KurtJacobson/alpha-spark/images/detector/20170306_222739.jpg

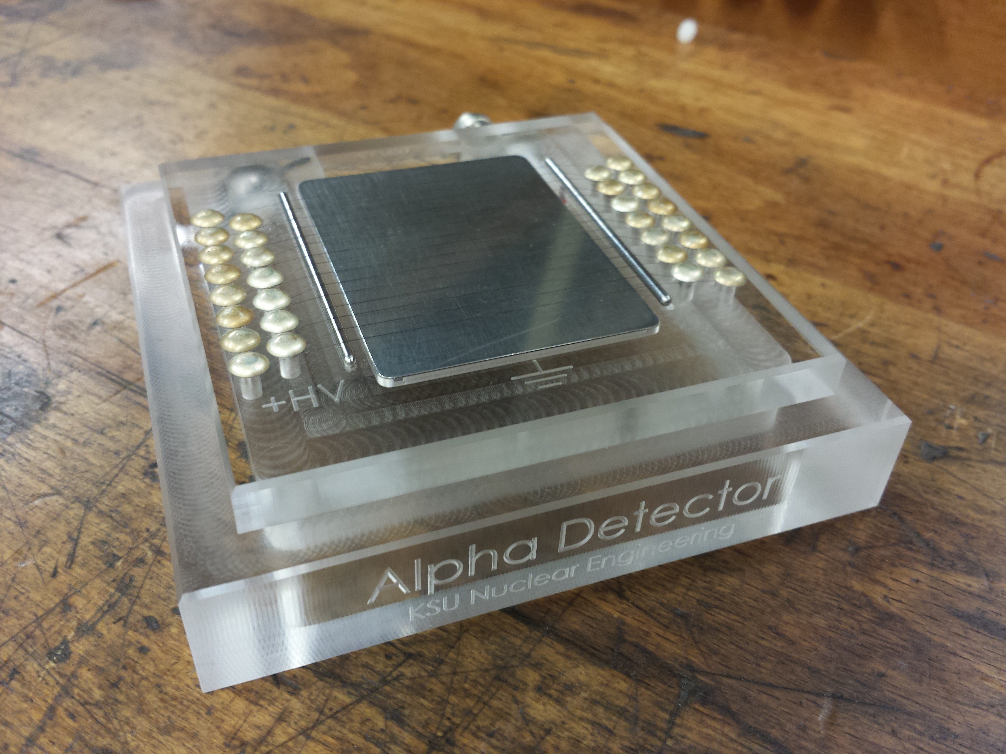
images/detector/20170306_222739.jpg
