KurtJacobson/alpha-spark/images/detector/20170306_222756.jpg

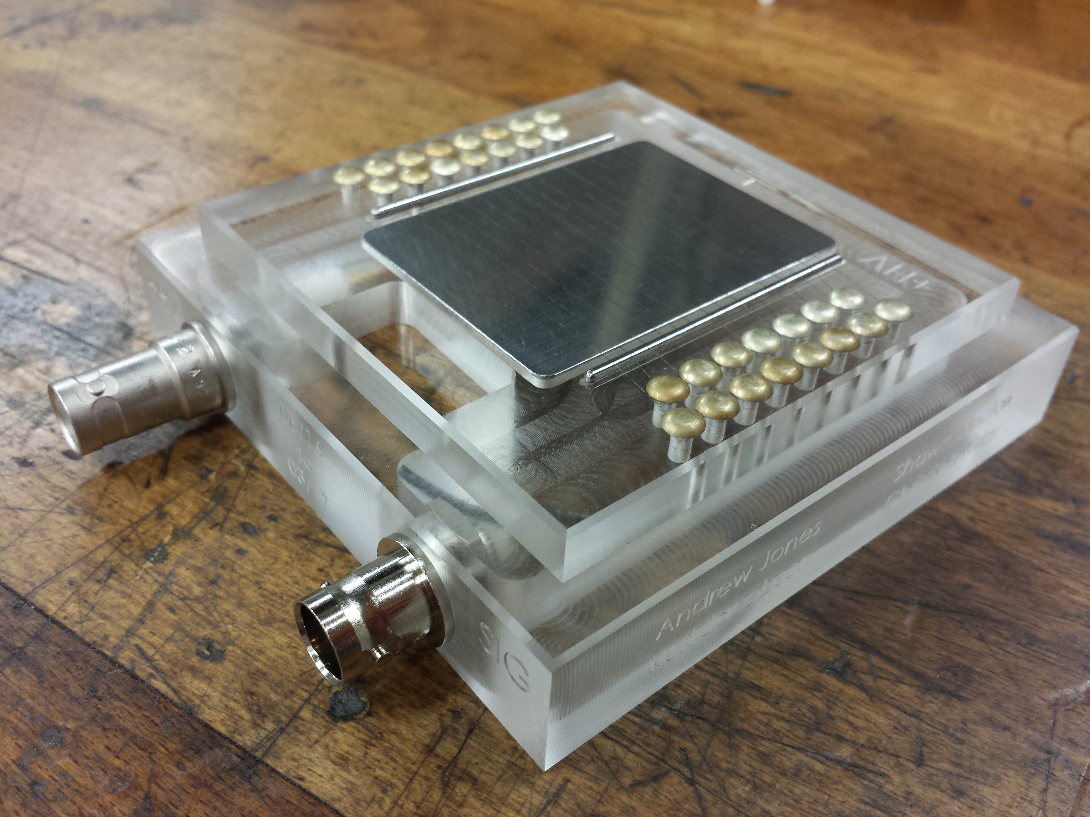
images/detector/20170306_222756.jpg
