KurtJacobson/alpha-spark/images/detector/20170306_222813.jpg

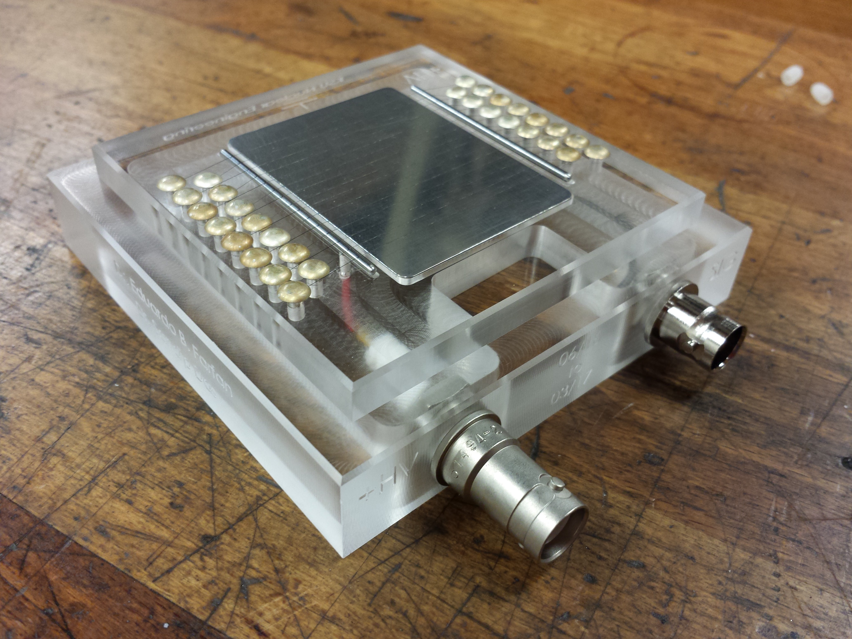
images/detector/20170306_222813.jpg
