KurtJacobson/alpha-spark/images/detector/20170322_160322.jpg

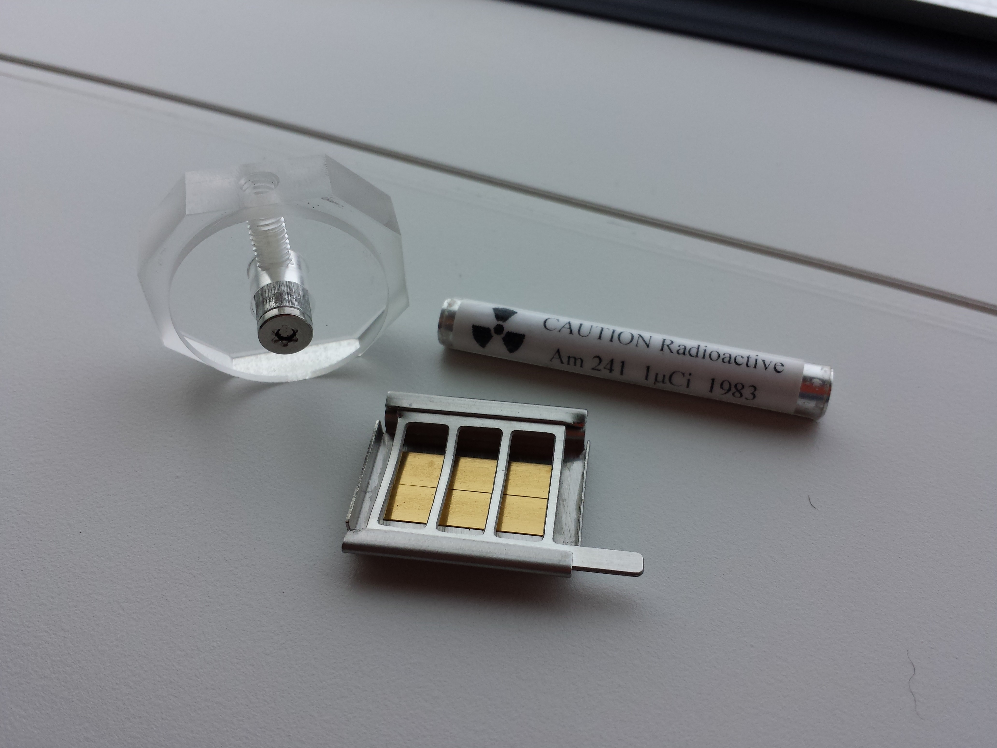
images/detector/20170322_160322.jpg
