KurtJacobson/alpha-spark/images/detector/20170322_160541.jpg

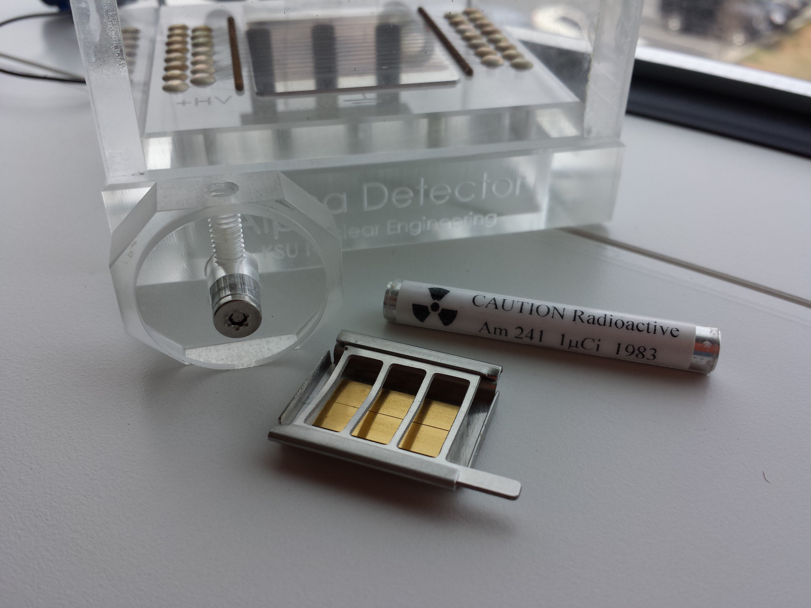
images/detector/20170322_160541.jpg
