KurtJacobson/alpha-spark/images/detector/DSC00182.jpg

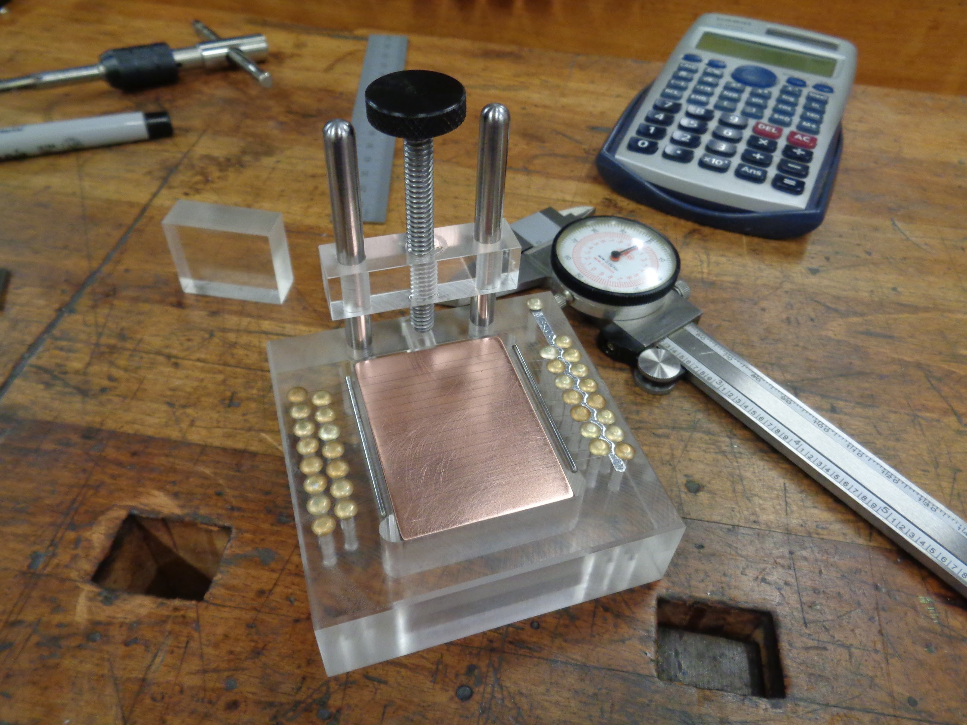
images/detector/DSC00182.jpg
