KurtJacobson/alpha-spark/images/detector/DSC00183.jpg

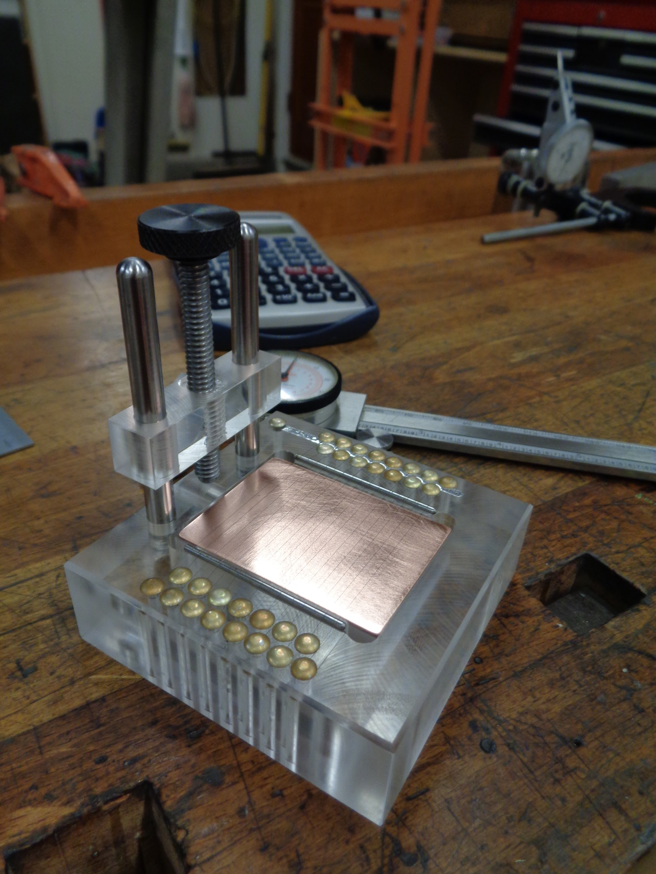
images/detector/DSC00183.jpg
