KurtJacobson/alpha-spark/images/detector/DSC00184.jpg

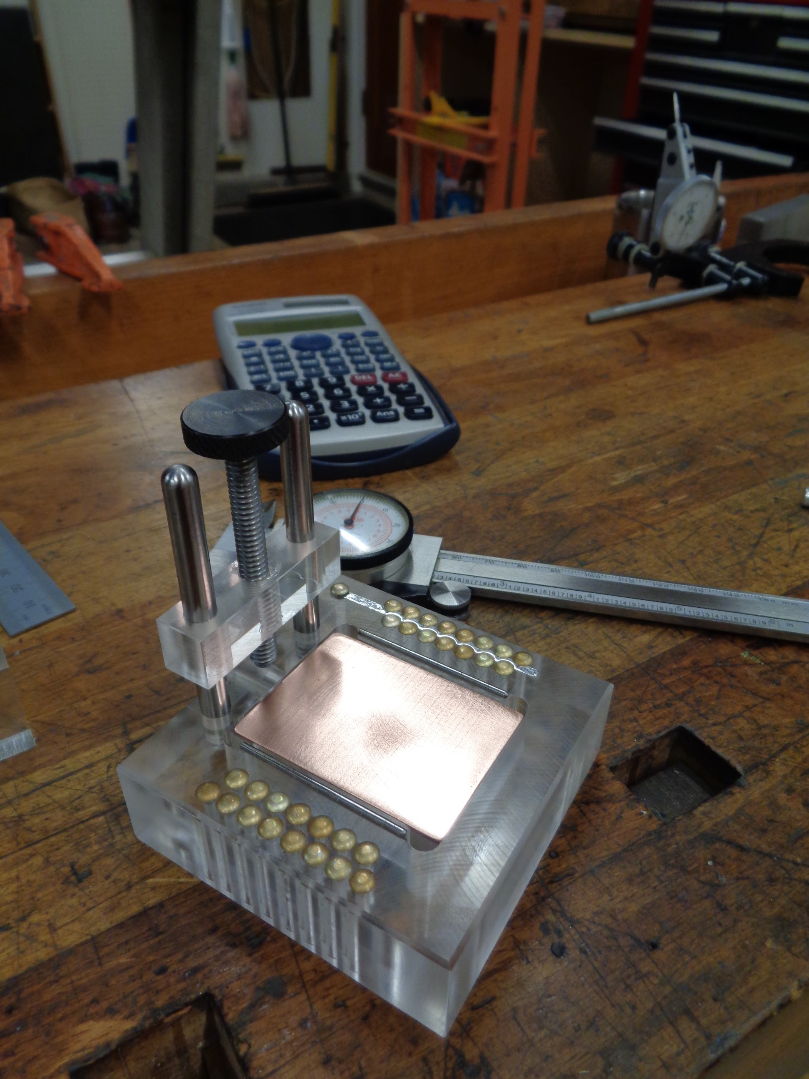
images/detector/DSC00184.jpg
