KurtJacobson/alpha-spark/images/detector/DSC00185.jpg

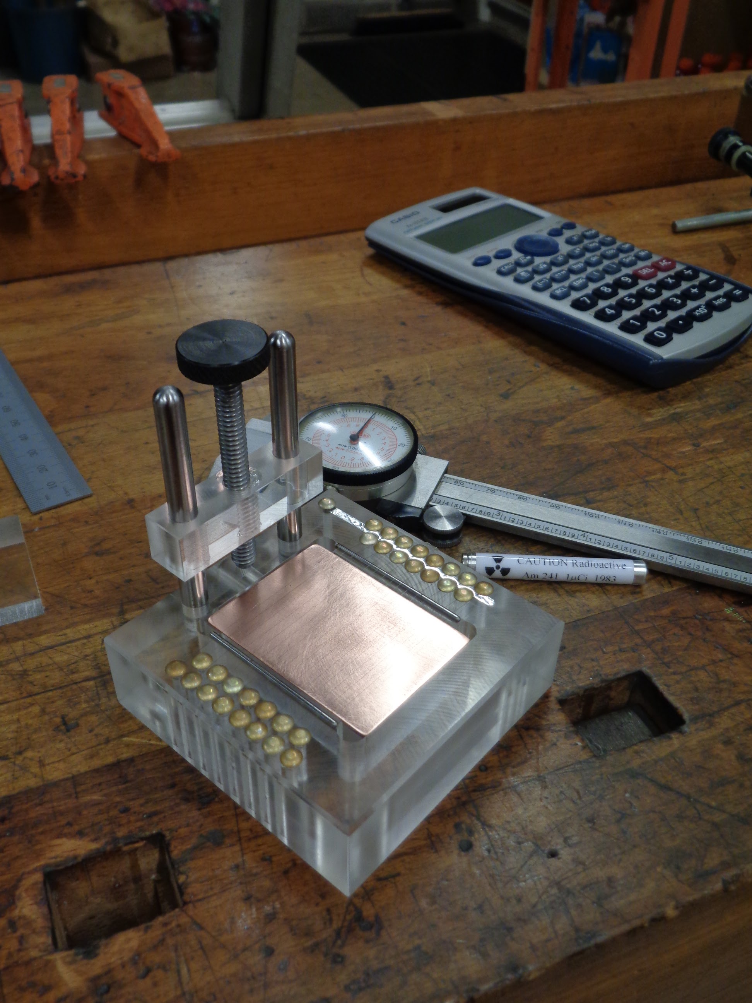
images/detector/DSC00185.jpg
