KurtJacobson/alpha-spark/images/detector/DSC00186.jpg

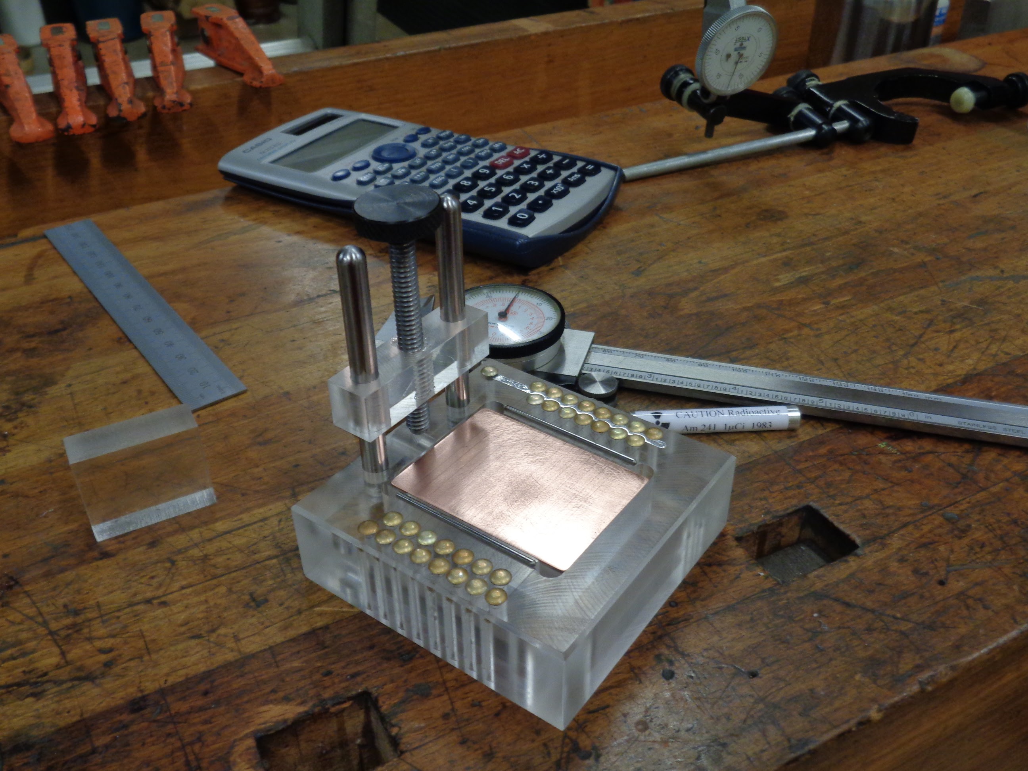
images/detector/DSC00186.jpg
