KurtJacobson/alpha-spark/images/detector/DSC00187.jpg

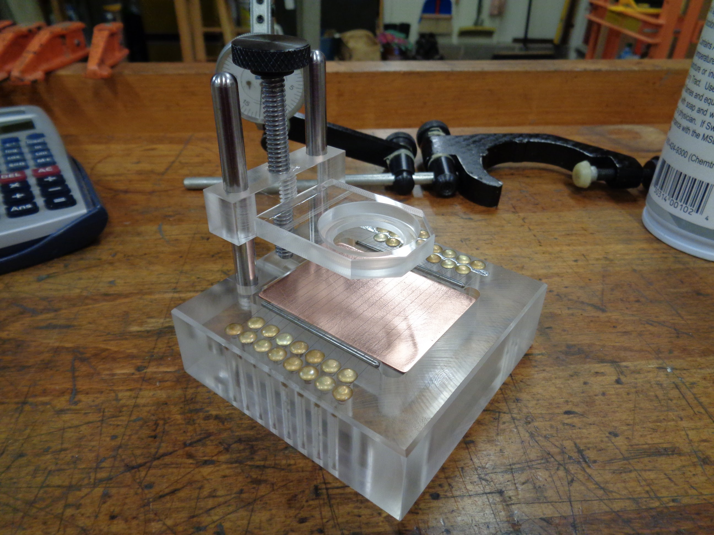
images/detector/DSC00187.jpg
