KurtJacobson/alpha-spark/images/detector/DSC00188.jpg

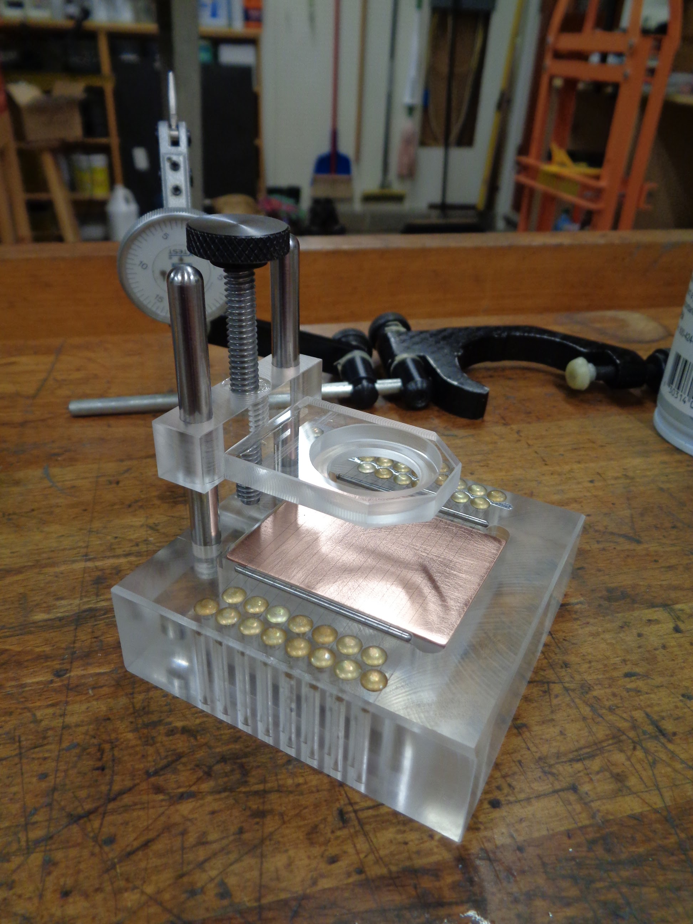
images/detector/DSC00188.jpg
