KurtJacobson/alpha-spark/images/detector/DSC00189.jpg

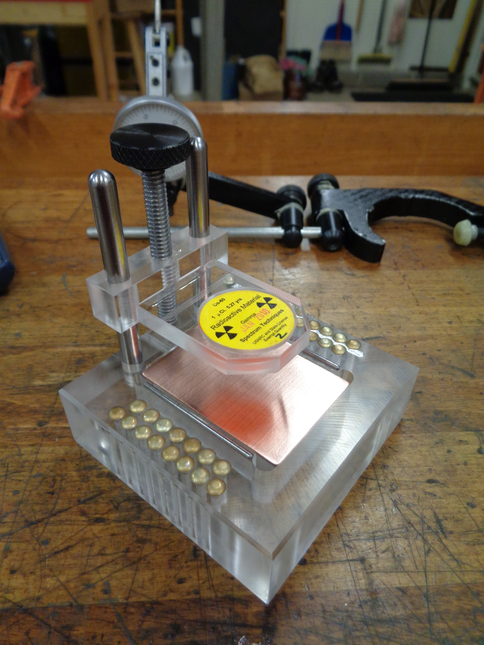
images/detector/DSC00189.jpg
