KurtJacobson/alpha-spark/images/detector/DSC00190.jpg

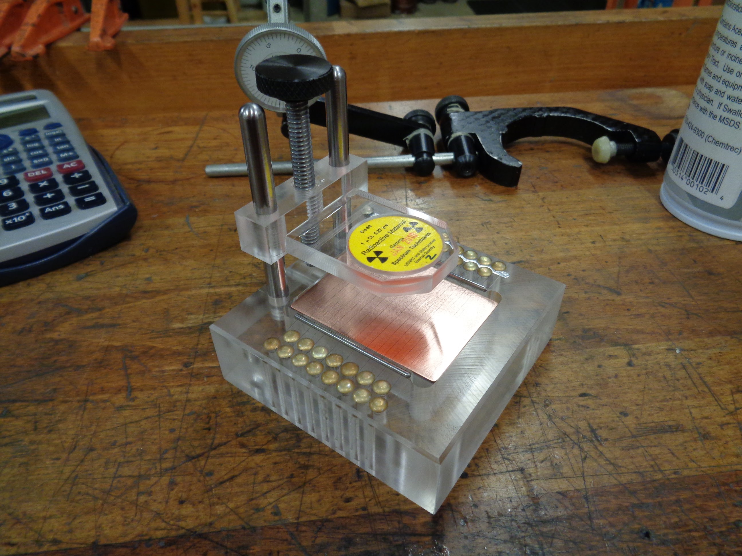
images/detector/DSC00190.jpg
