KurtJacobson/alpha-spark/images/detector/DSC00191.jpg

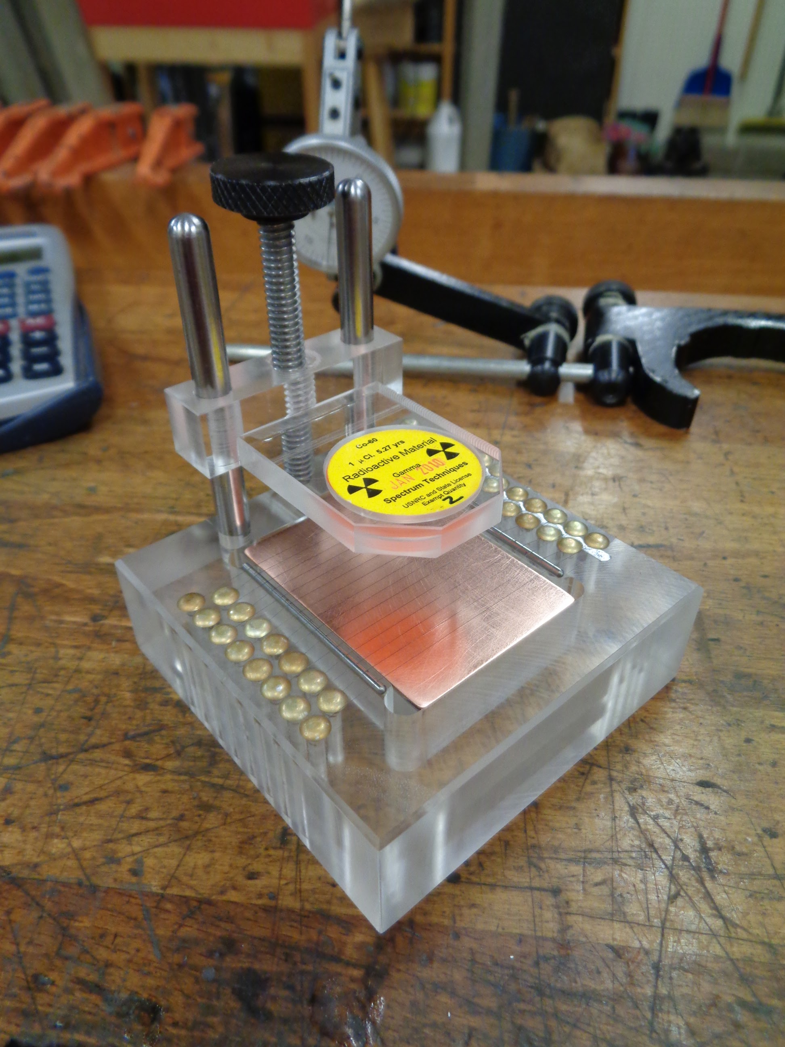
images/detector/DSC00191.jpg
