KurtJacobson/alpha-spark/images/detector/DSC00192.jpg

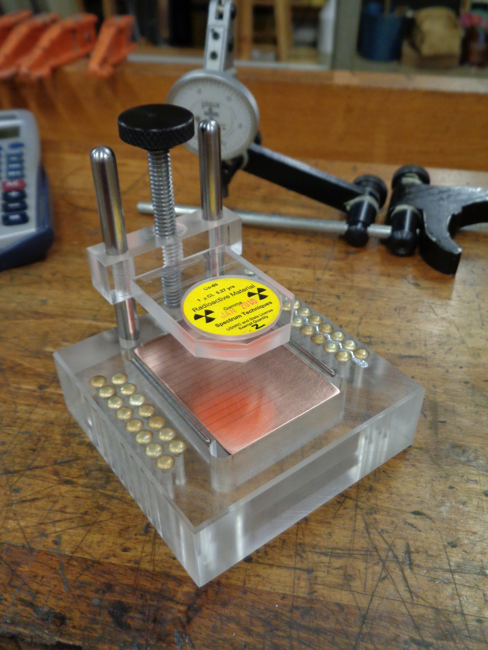
images/detector/DSC00192.jpg
