KurtJacobson/alpha-spark/images/detector/DSC00193.jpg

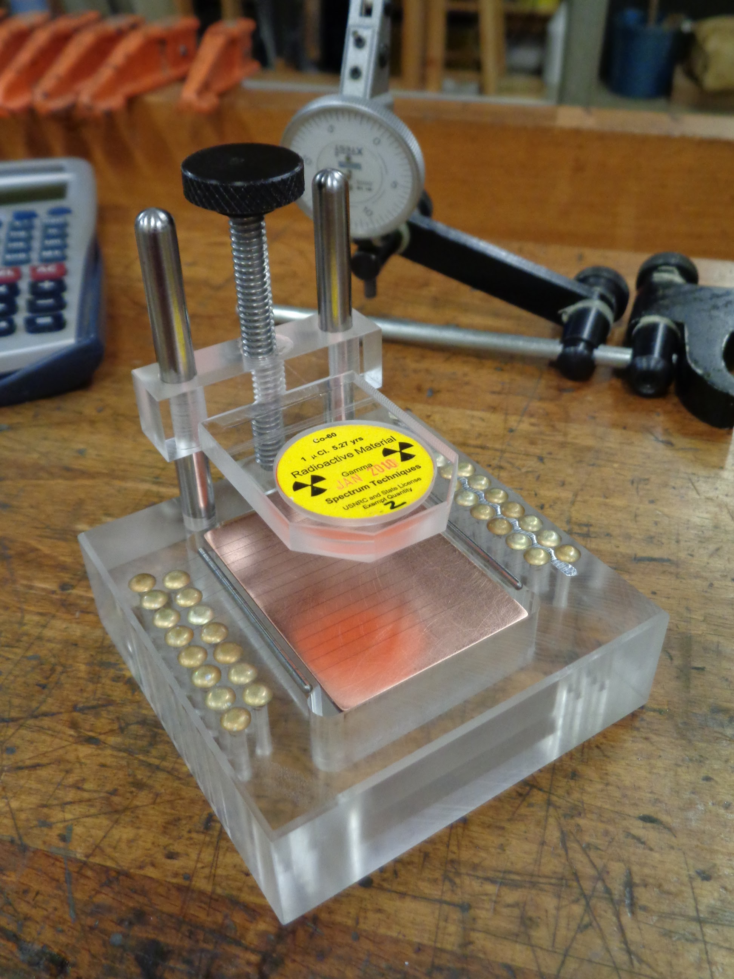
images/detector/DSC00193.jpg
