KurtJacobson/alpha-spark/images/pulses/scope_0.bmp

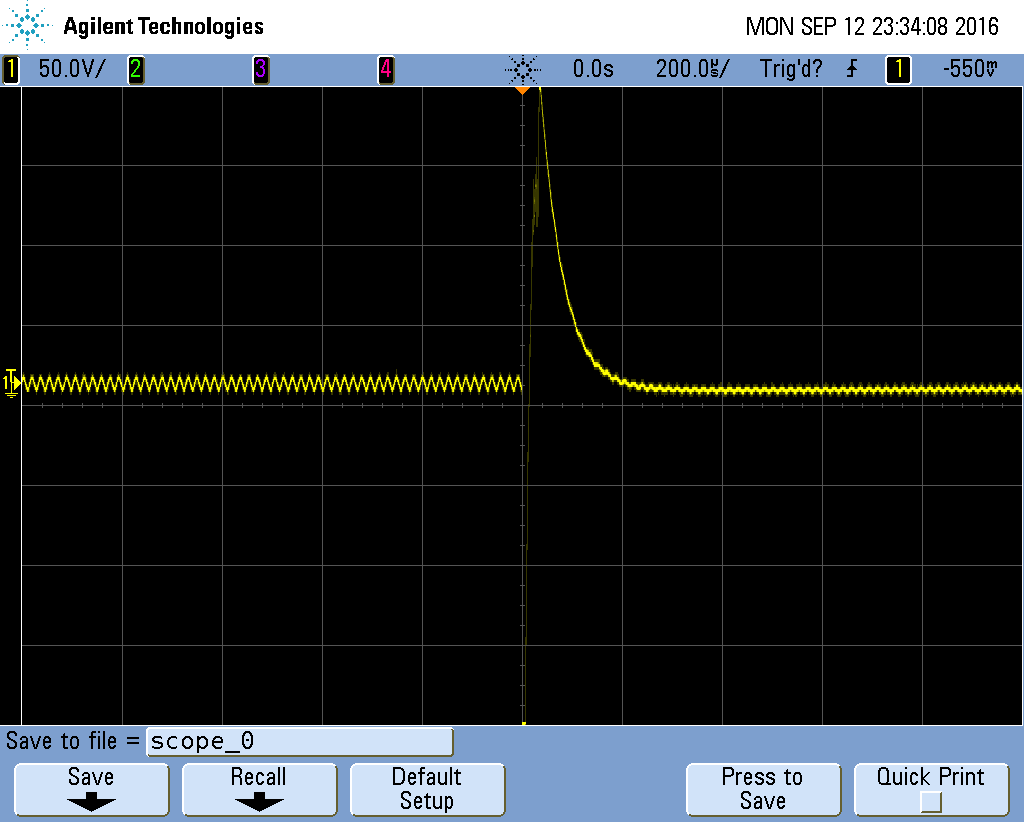
images/pulses/scope_0.bmp
