KurtJacobson/alpha-spark/images/pulses/scope_3.bmp

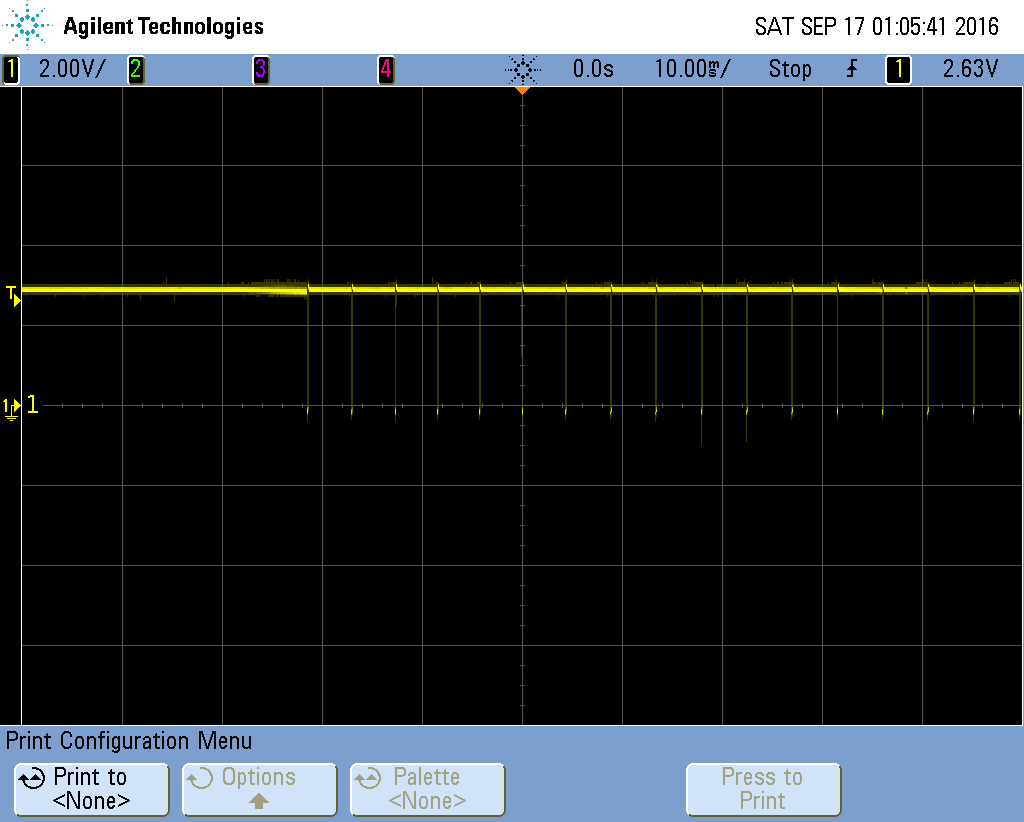
images/pulses/scope_3.bmp
