KurtJacobson/alpha-spark/images/pulses/scope_4.bmp

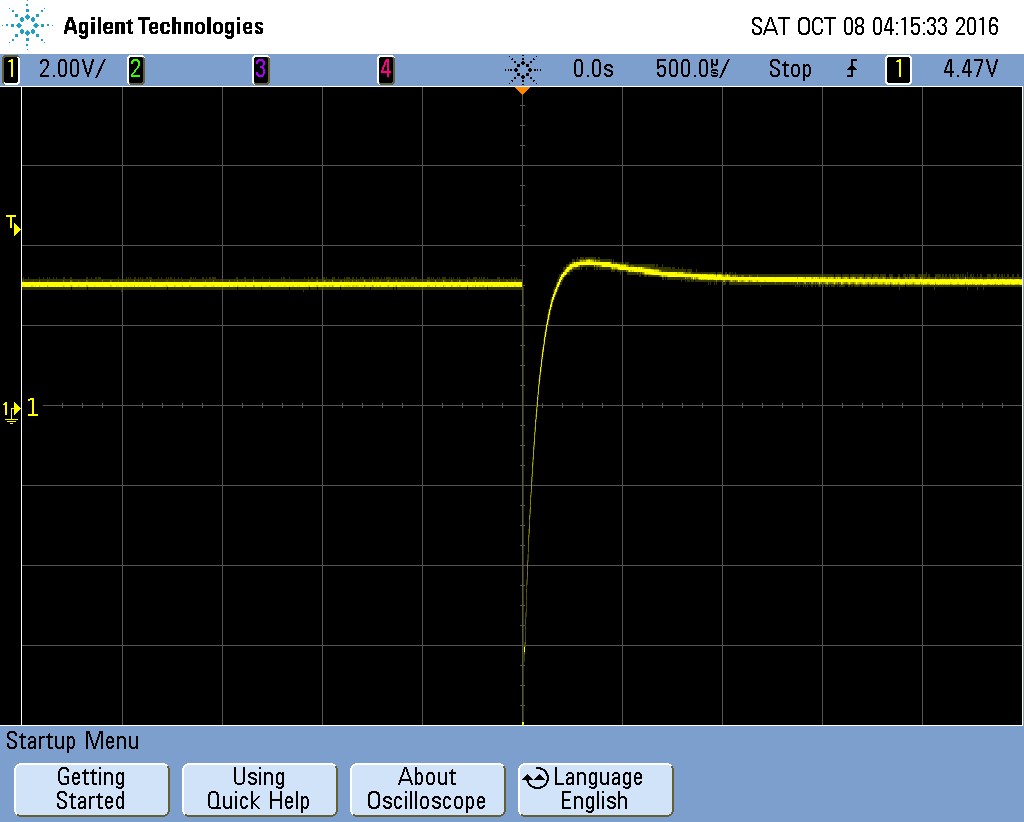
images/pulses/scope_4.bmp
