KurtJacobson/alpha-spark/images/pulses/scope_5.bmp

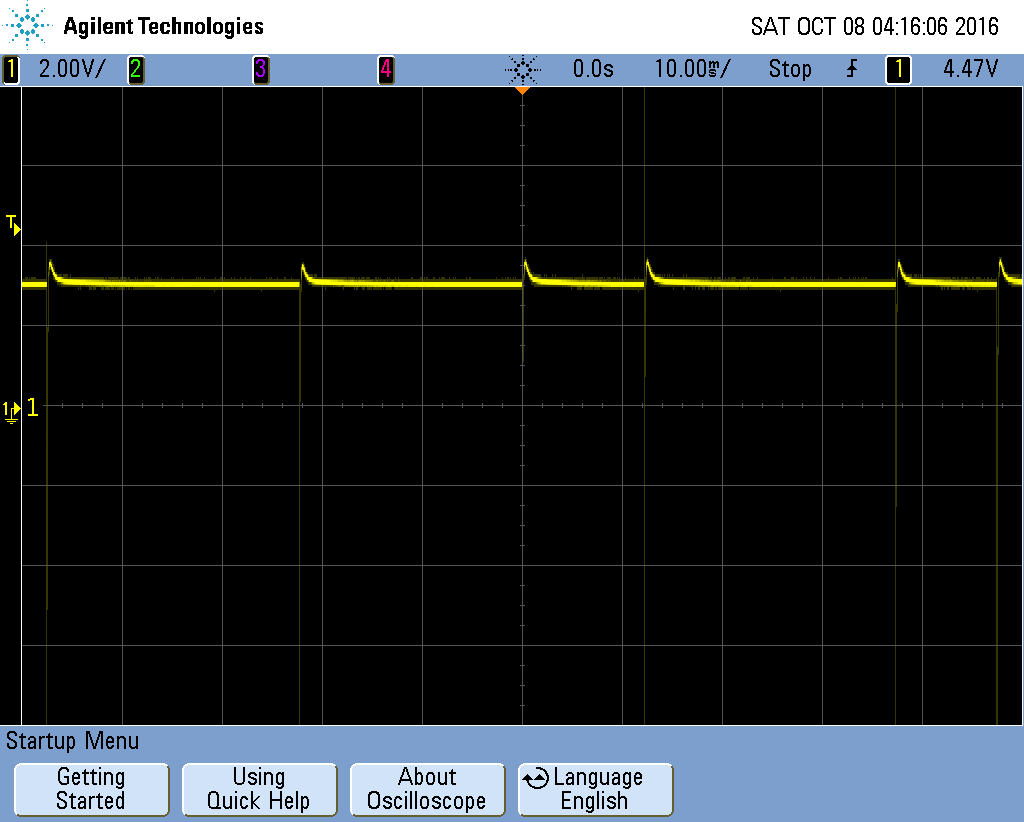
images/pulses/scope_5.bmp
