KurtJacobson/alpha-spark/images/pulses/scope_10.bmp

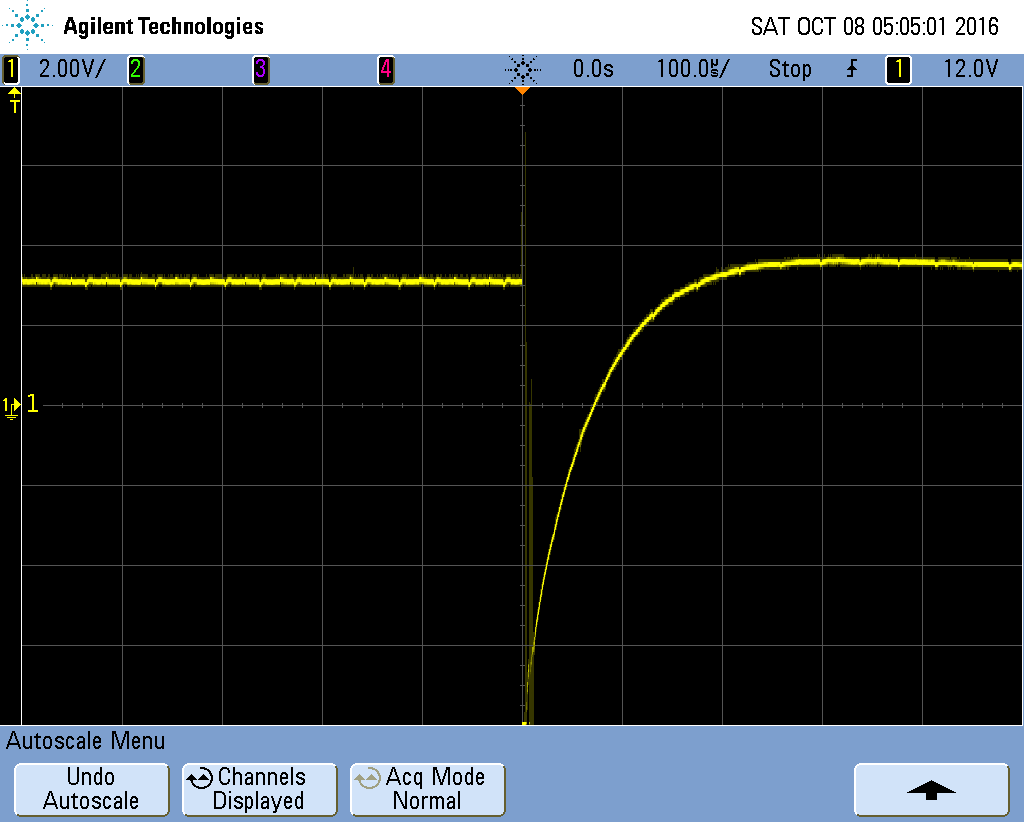
images/pulses/scope_10.bmp
