KurtJacobson/alpha-spark/images/pulses/scope_11.bmp

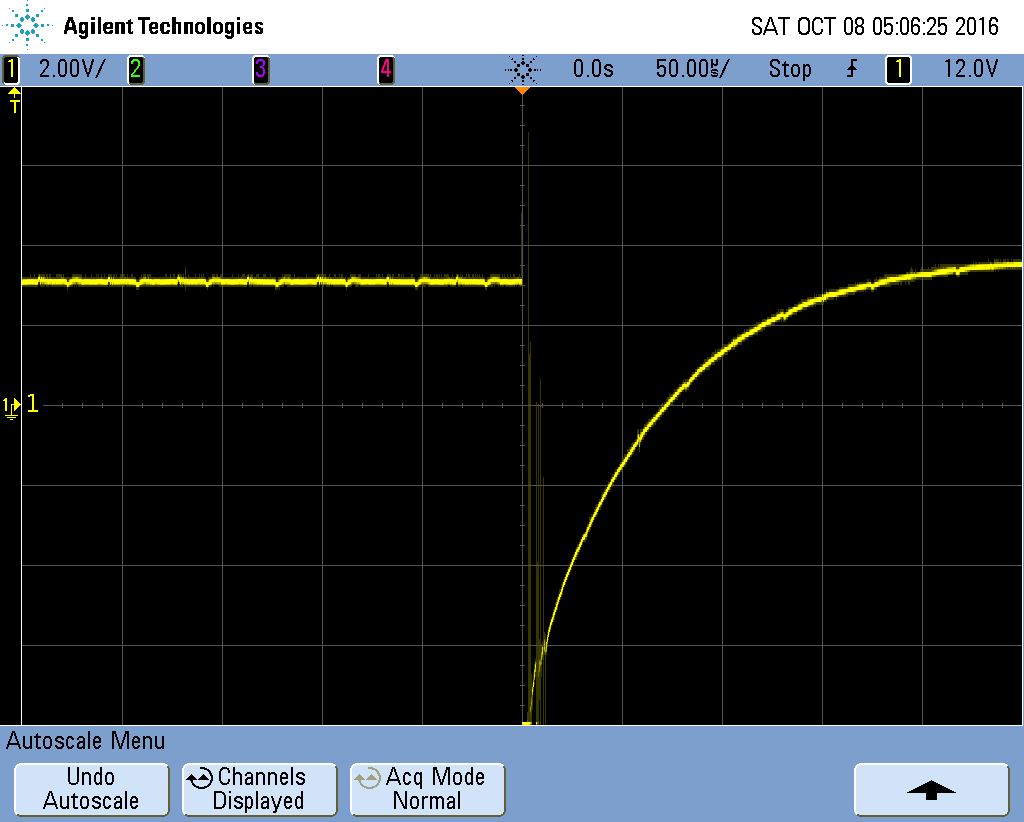
images/pulses/scope_11.bmp
