KurtJacobson/alpha-spark/models/CCS Final.png

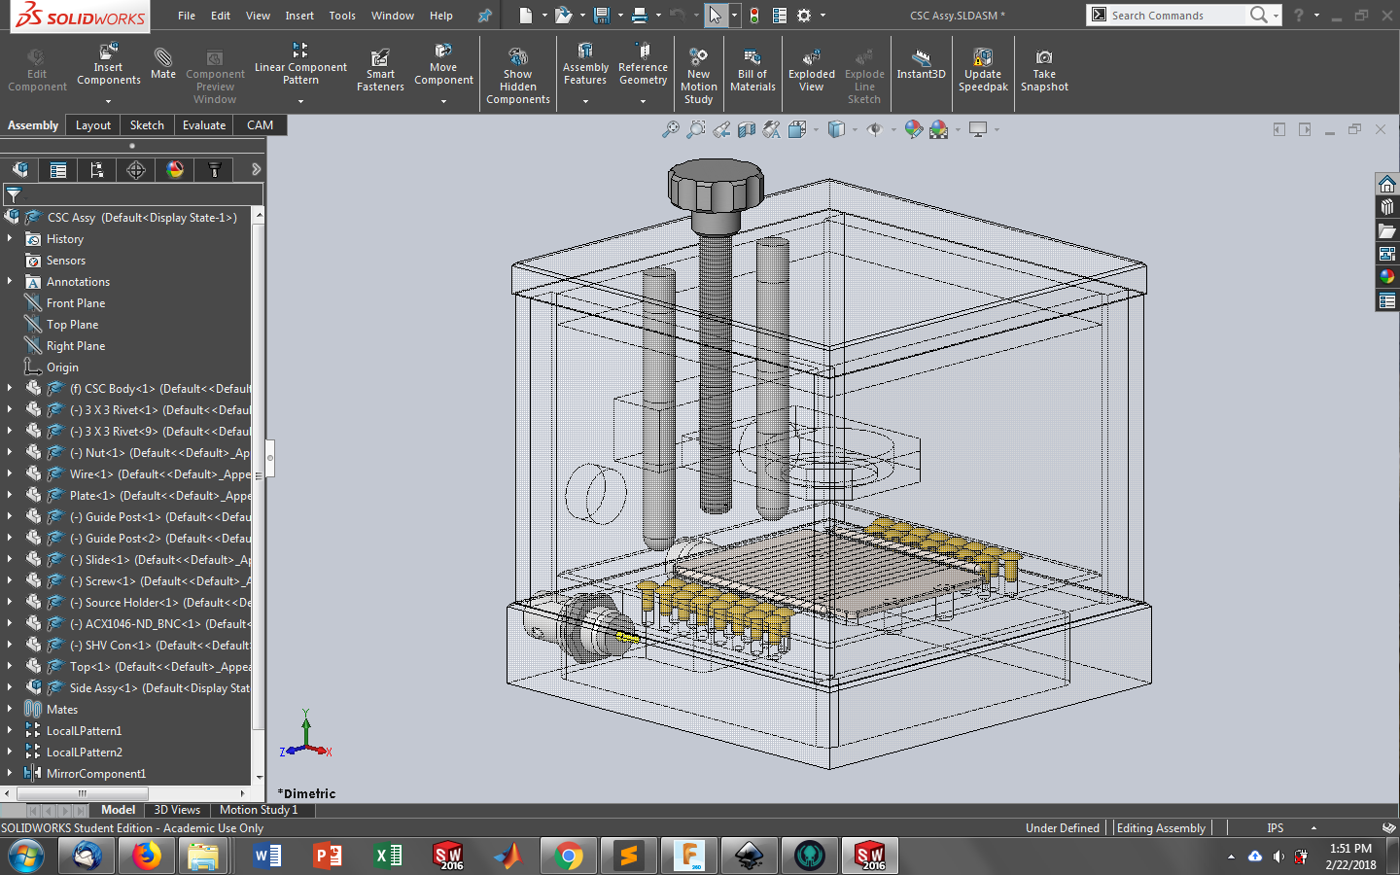
models/CCS Final.png
