KurtJacobson/alpha-spark/models/CCS w Holder Dia.png

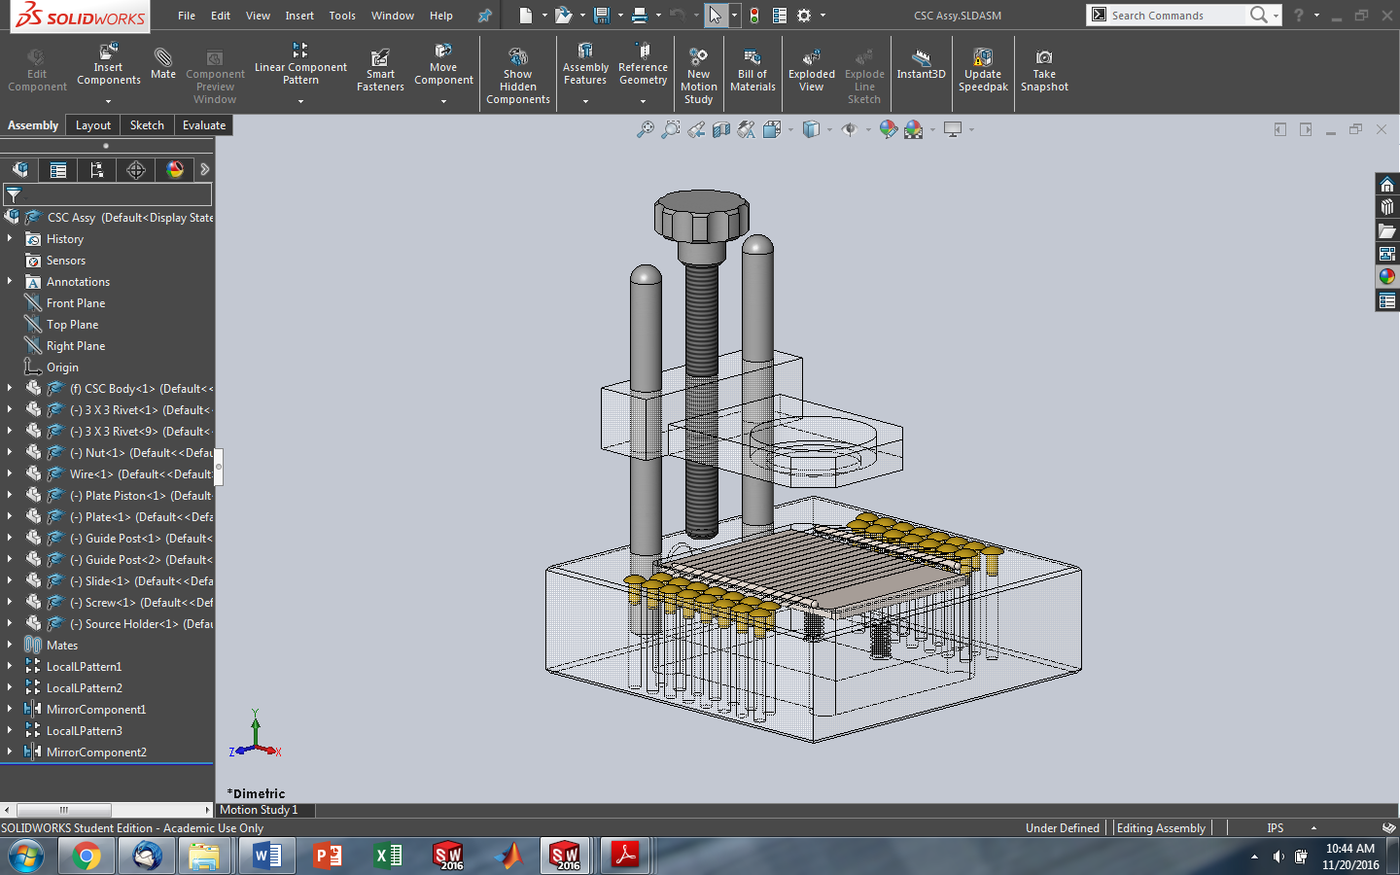
models/CCS w Holder Dia.png
