KurtJacobson/alpha-spark/models/CCS w Holder Iso.png

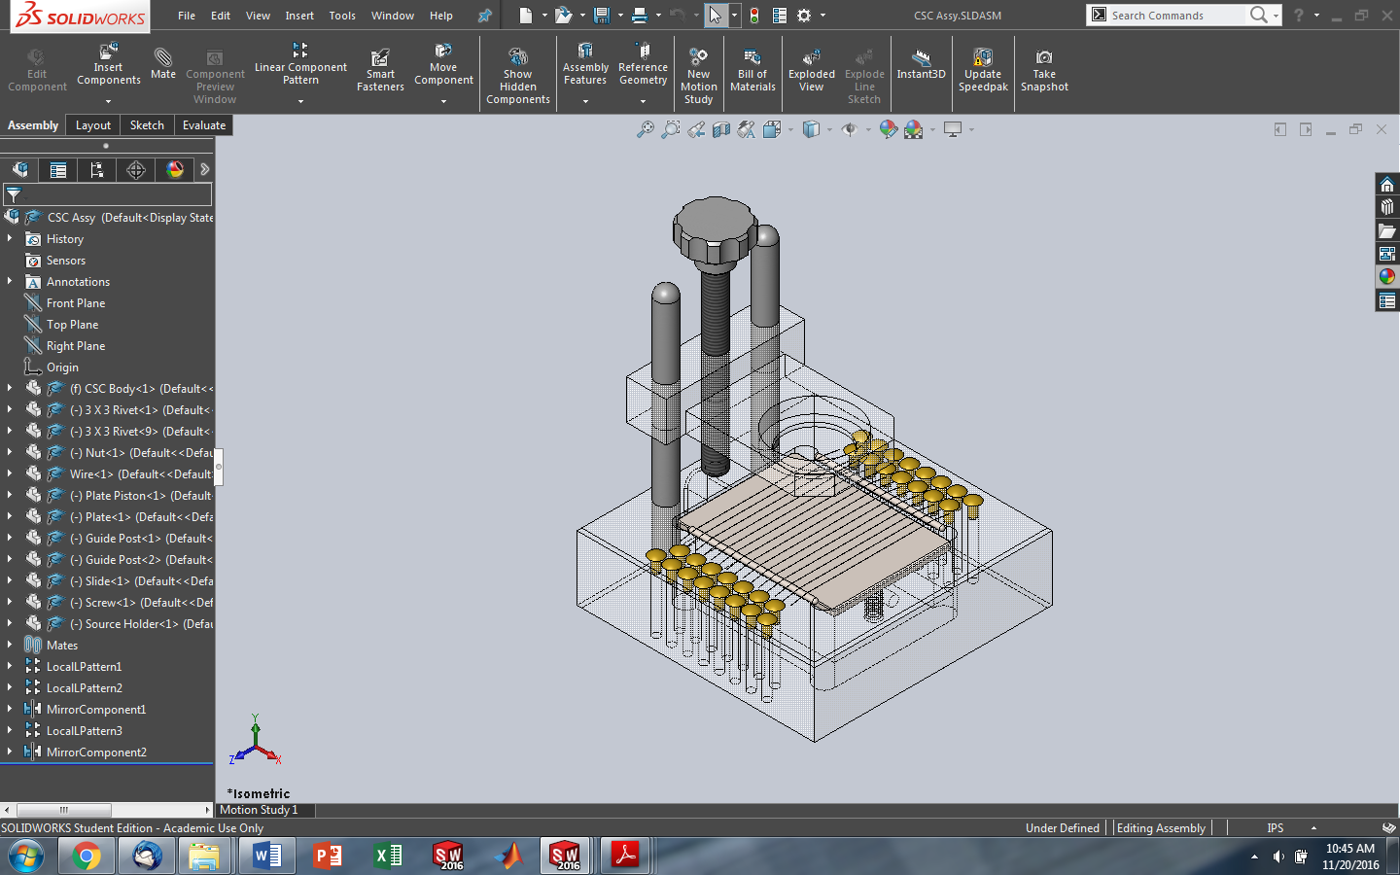
models/CCS w Holder Iso.png
