KurtJacobson/alpha-spark/models/CSC Model Dia.png

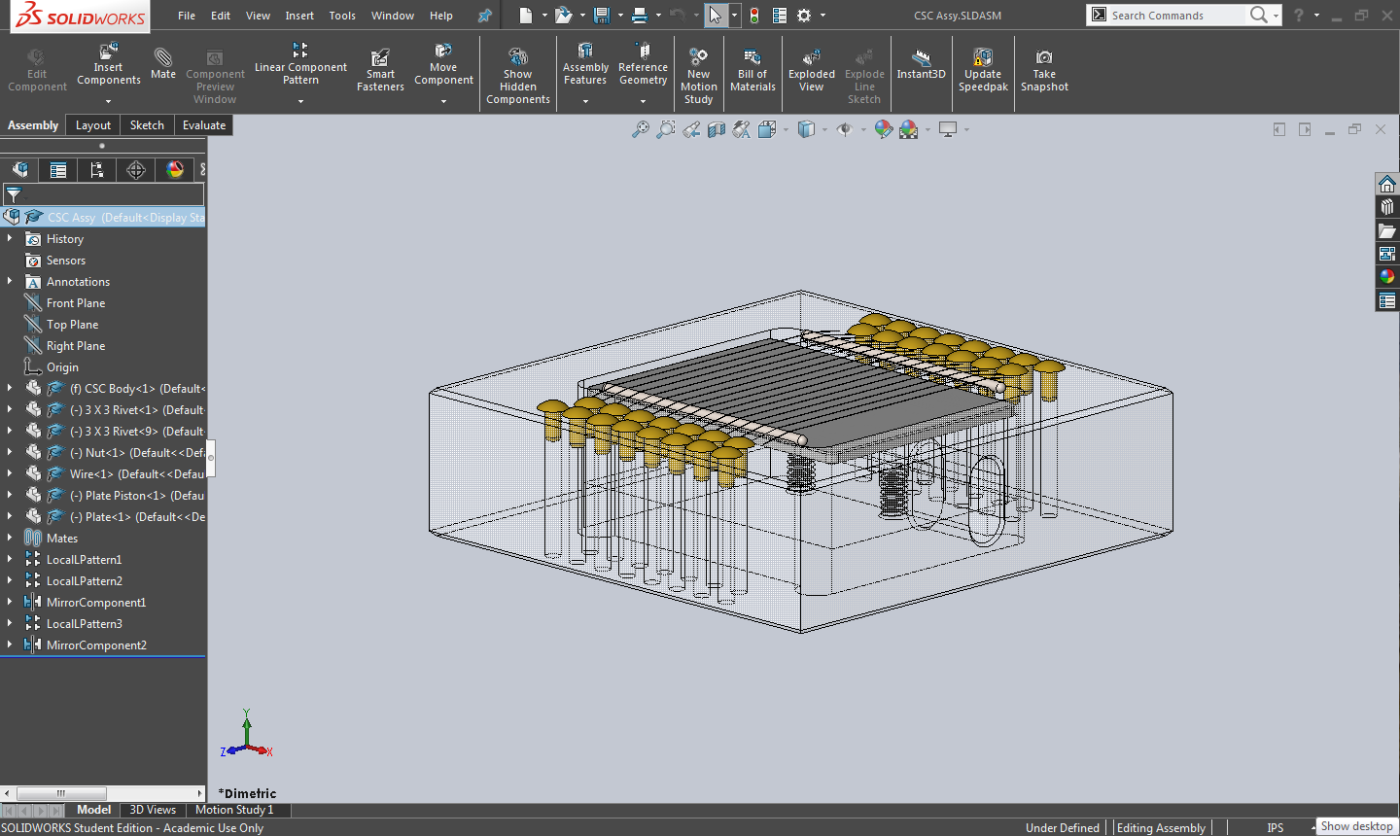
models/CSC Model Dia.png
