KurtJacobson/alpha-spark/models/CSC Model Iso.png

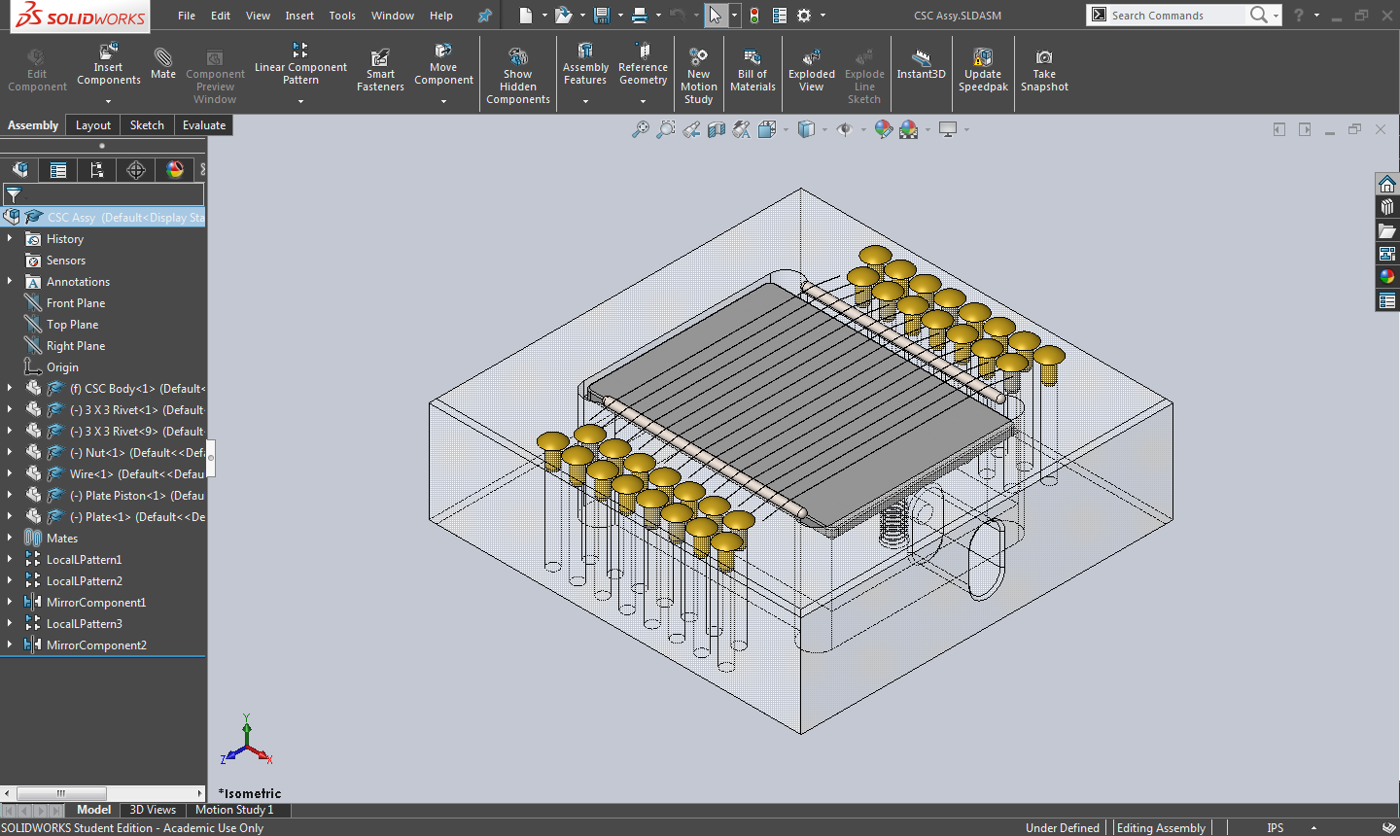
models/CSC Model Iso.png
