KurtJacobson/alpha-spark/models/CSC Render.JPG

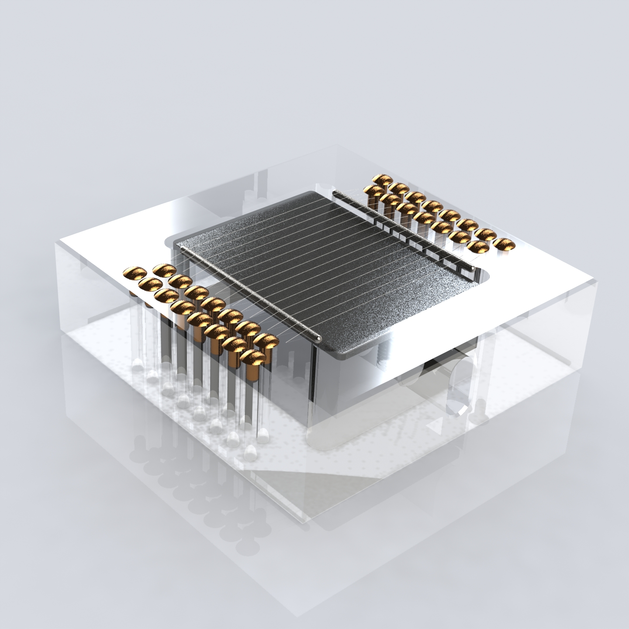
models/CSC Render.JPG
