KurtJacobson/alpha-spark/models/1st Build/Source.SLDPRT

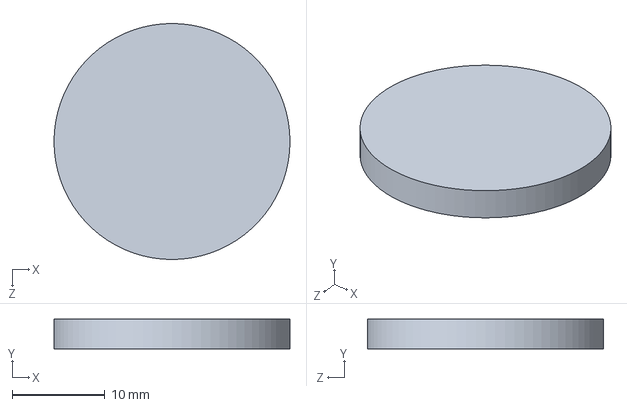
[picture p48: CAD file, 2018-02-22]
models/1st Build/Source.SLDPRT
25.4 x 3.17 x 25.4 mm
