KurtJacobson/alpha-spark/models/2nd Build/Slide.SLDPRT

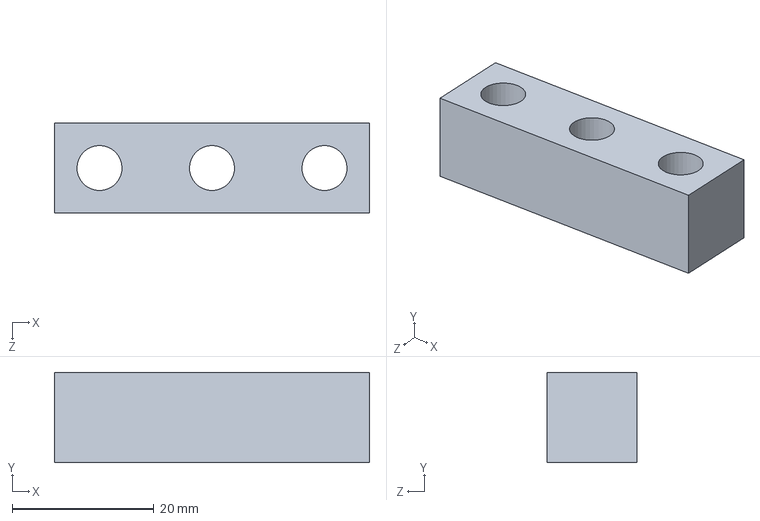
[picture p49: CAD file, 2018-02-22]
models/2nd Build/Slide.SLDPRT
44.5 x 12.7 x 12.7 mm
