KurtJacobson/alpha-spark/models/1st Build/Plate.SLDPRT

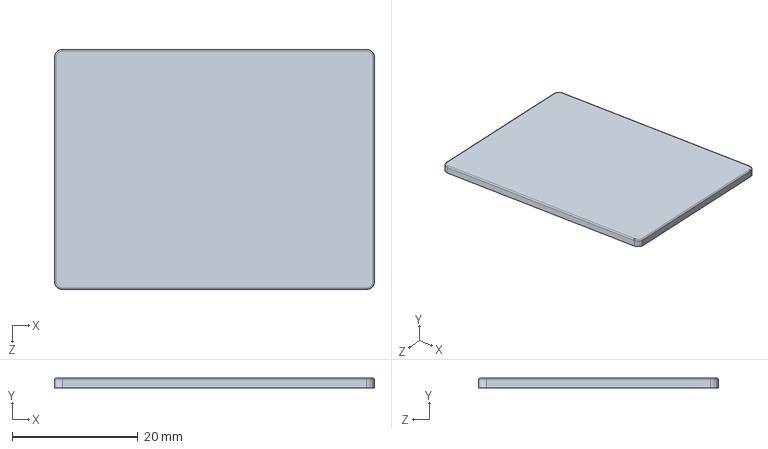
[picture p50: CAD file, 2018-02-22]
models/1st Build/Plate.SLDPRT
50.8 x 1.59 x 38.1 mm
