KurtJacobson/alpha-spark/models/2nd Build/SHV.SLDPRT

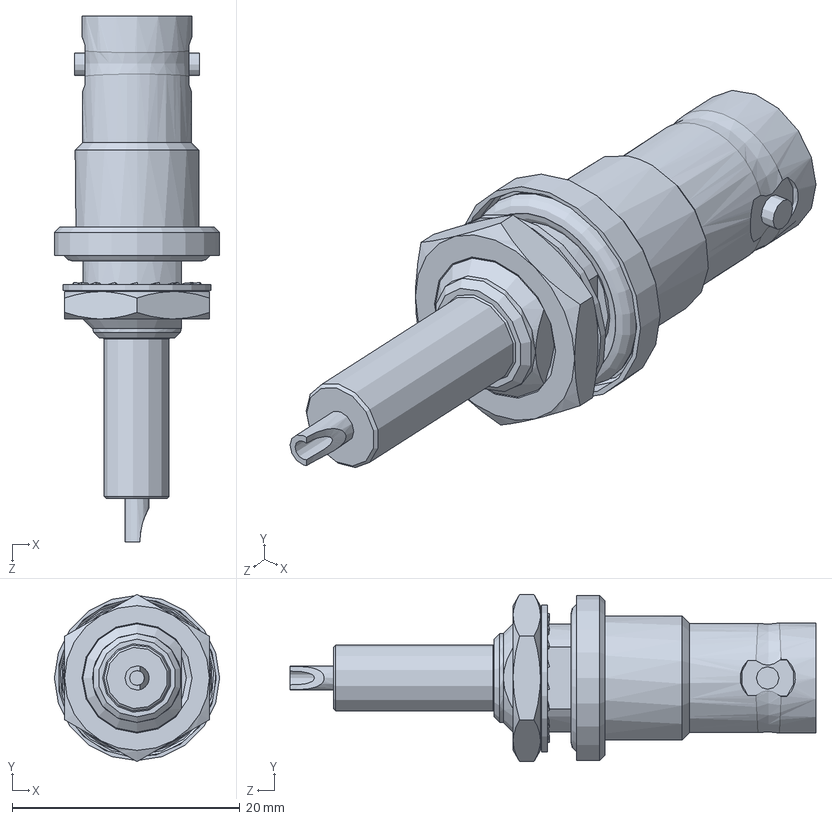
[picture p51: CAD file, 2018-02-22]
models/2nd Build/SHV.SLDPRT
14.5 x 14.7 x 46.1 mm
