KurtJacobson/alpha-spark/models/2nd Build/Top Cover.SLDPRT

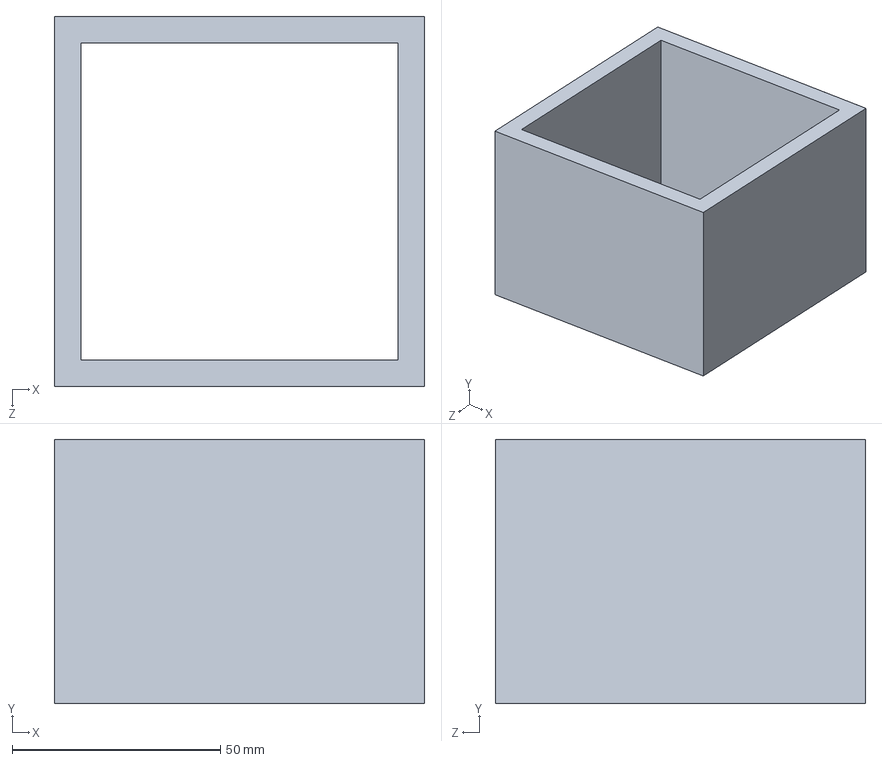
[picture p52: CAD file, 2018-02-22]
models/2nd Build/Top Cover.SLDPRT
88.9 x 63.5 x 88.9 mm
