KurtJacobson/alpha-spark/models/1st Build/Plate Piston.SLDPRT

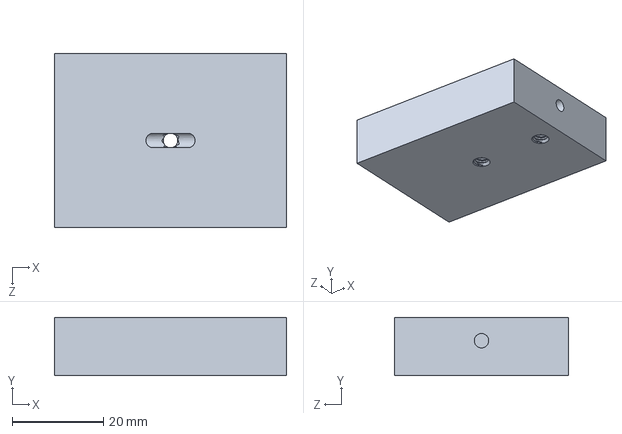
[picture p53: CAD file, 2018-02-22]
models/1st Build/Plate Piston.SLDPRT
50.8 x 12.7 x 38.1 mm
