KurtJacobson/alpha-spark/models/2nd Build/Plate.SLDPRT

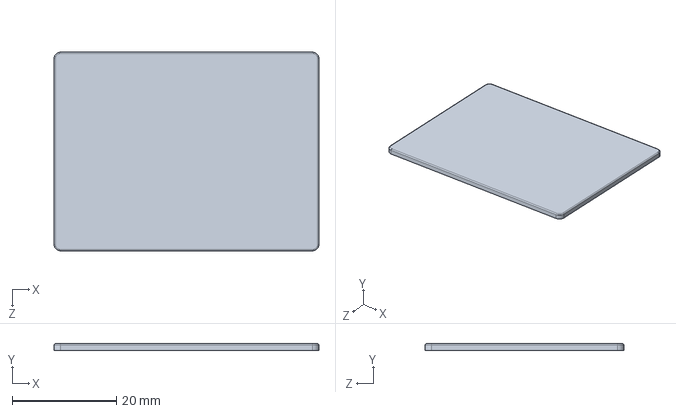
[picture p54: CAD file, 2018-02-22]
models/2nd Build/Plate.SLDPRT
50.8 x 1.27 x 38.1 mm
