KurtJacobson/alpha-spark/models/2nd Build/Wire.SLDPRT

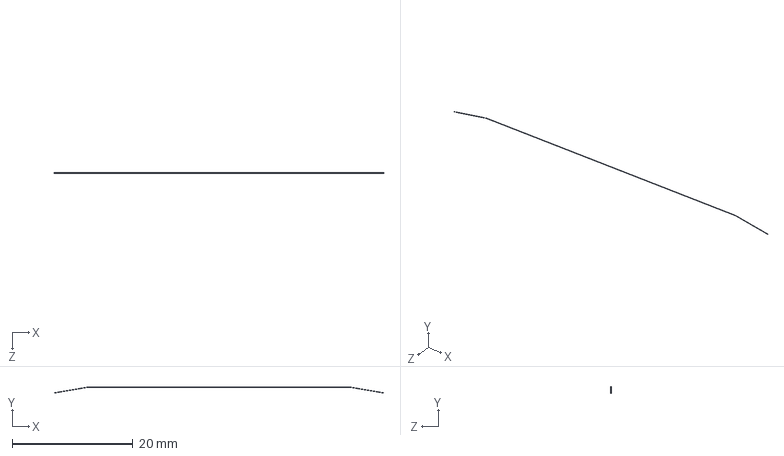
[picture p55: CAD file, 2018-02-22]
models/2nd Build/Wire.SLDPRT
54.4 x 1.01 x 0.0508 mm
