KurtJacobson/alpha-spark/models/2nd Build/Side.SLDPRT

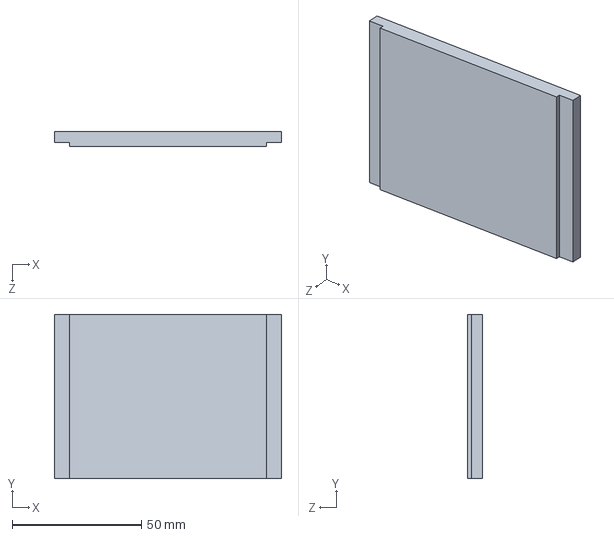
[picture p56: CAD file, 2018-02-22]
models/2nd Build/Side.SLDPRT
87.9 x 63.5 x 5.84 mm
