KurtJacobson/alpha-spark/models/2nd Build/Guide Post.SLDPRT

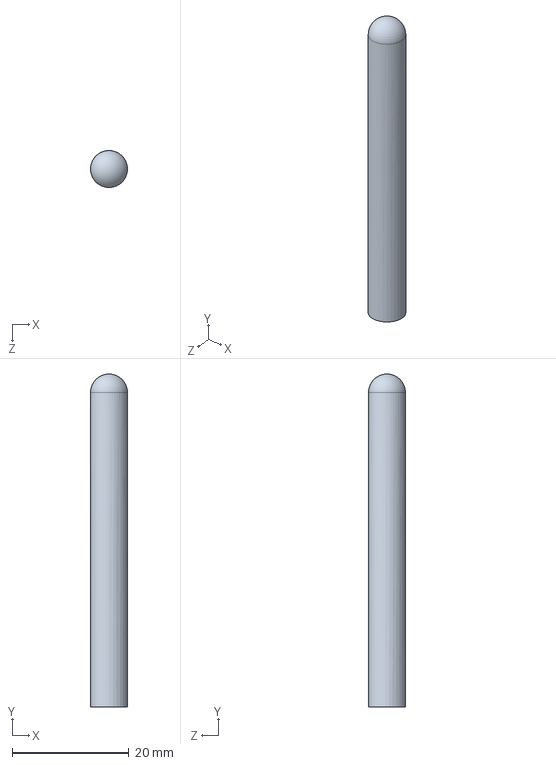
[picture p57: CAD file, 2018-02-22]
models/2nd Build/Guide Post.SLDPRT
6.35 x 57.1 x 6.35 mm
