KurtJacobson/alpha-spark/models/2nd Build/ACX1046-ND_BNC.SLDPRT

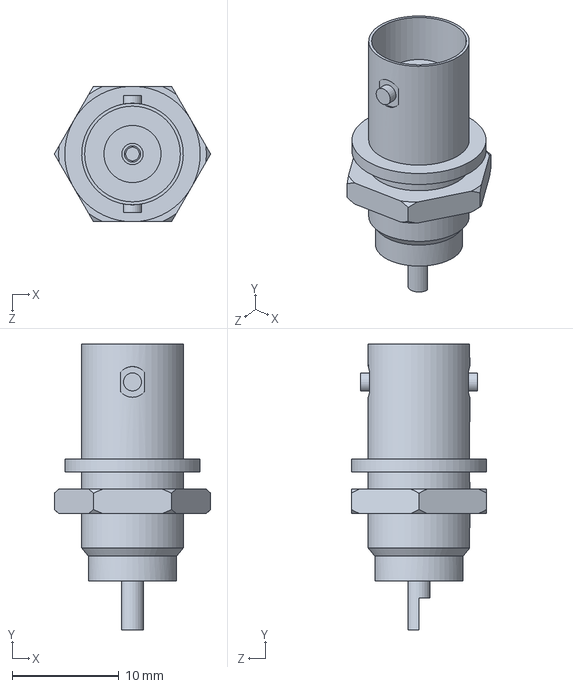
[picture p58: CAD file, 2018-02-22]
models/2nd Build/ACX1046-ND_BNC.SLDPRT
14.7 x 26.8 x 12.7 mm
